hristovp/Key60/KiKad/Keyboard-60%/AlexandriaLibrary-master/graphics/acheronLongExtended.png

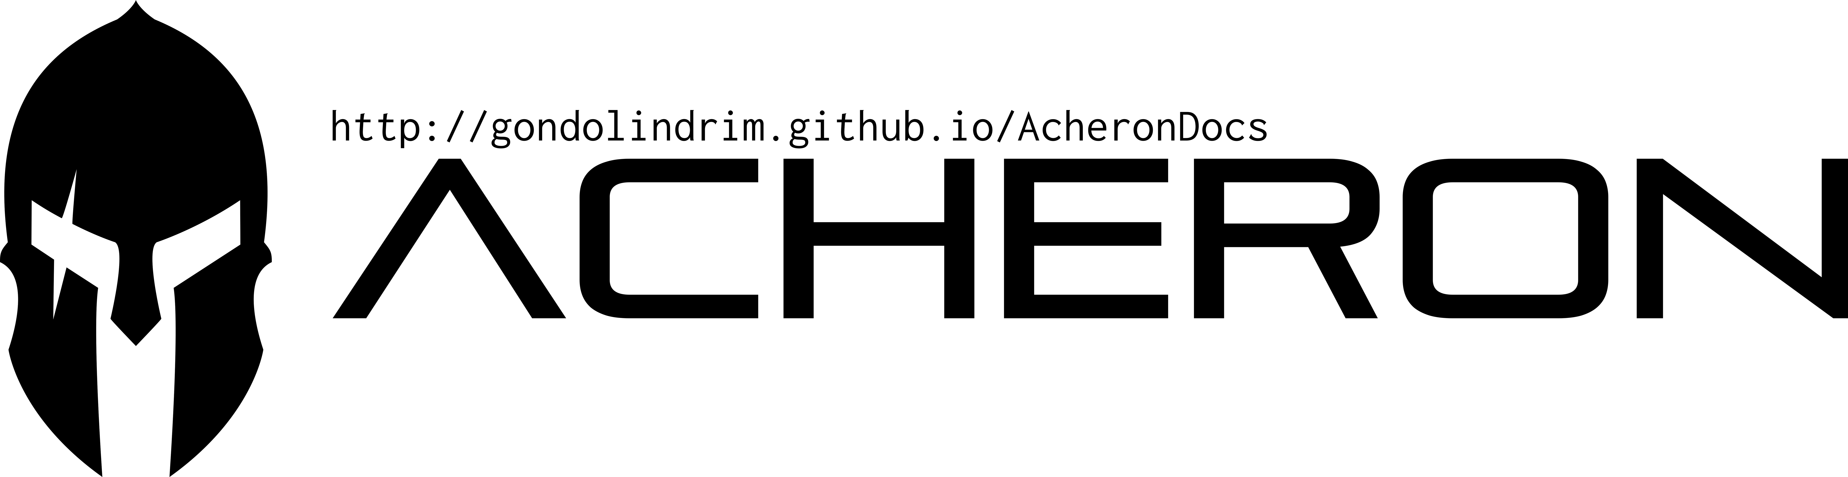
KiKad/Keyboard-60%/AlexandriaLibrary-master/graphics/acheronLongExtended.png
