hristovp/Key60/KiKad/Keyboard-60%/AlexandriaLibrary-master/graphics/acheronReadme.png

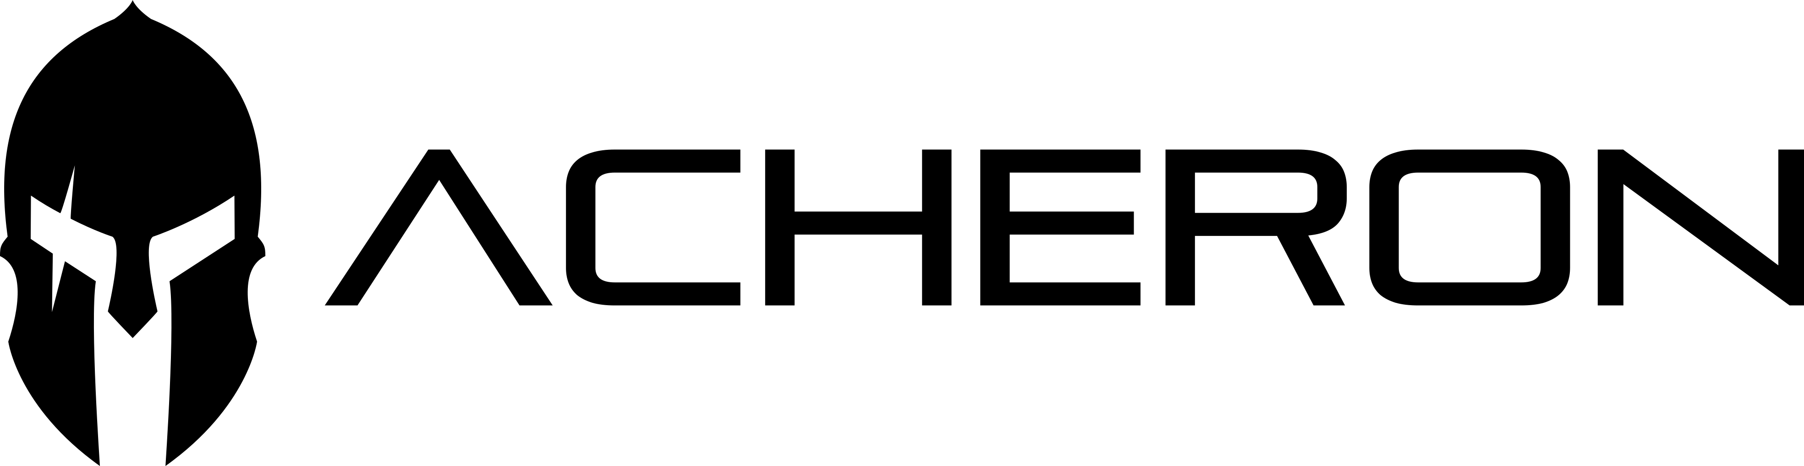
KiKad/Keyboard-60%/AlexandriaLibrary-master/graphics/acheronReadme.png
