hristovp/Key60/KiKad/Keyboard-60%/AlexandriaLibrary-master/graphics/acheronShort.png

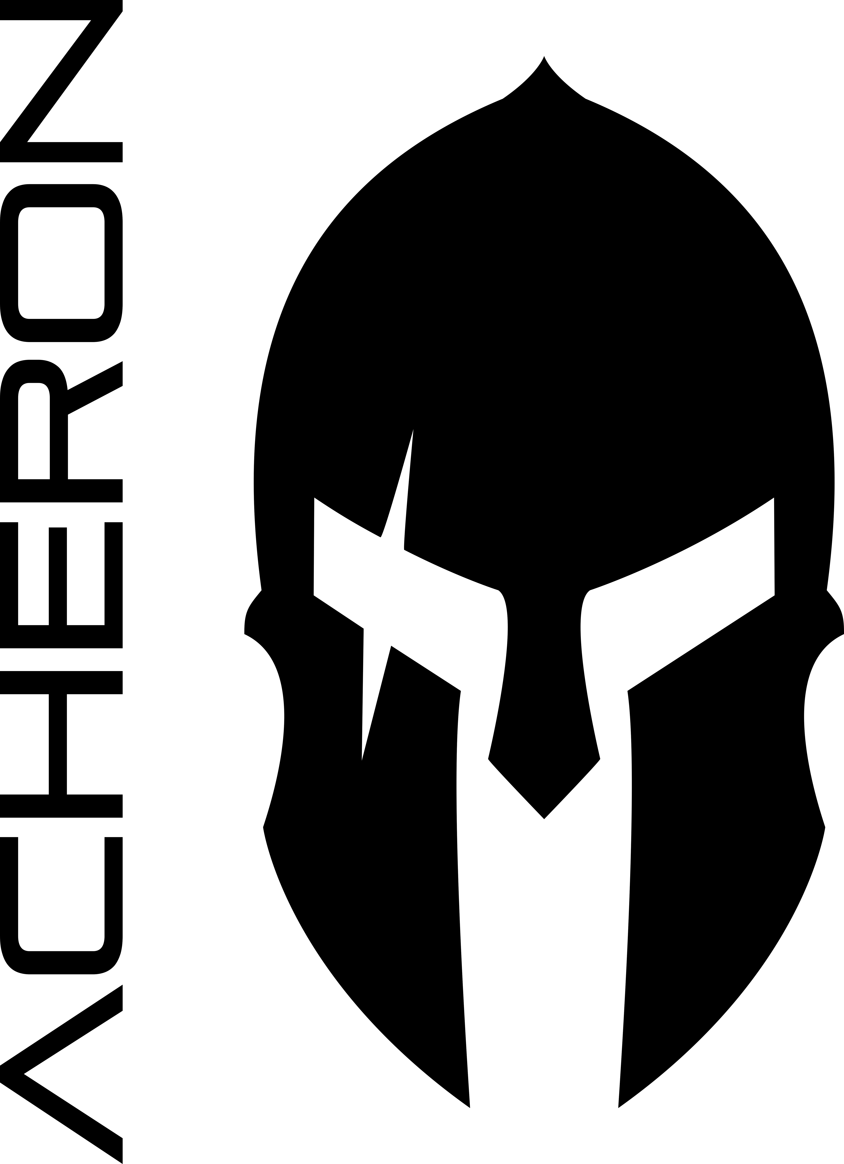
KiKad/Keyboard-60%/AlexandriaLibrary-master/graphics/acheronShort.png
