hristovp/Key60/KiKad/Keyboard-60%/AlexandriaLibrary-master/graphics/e6c1209rgb.png

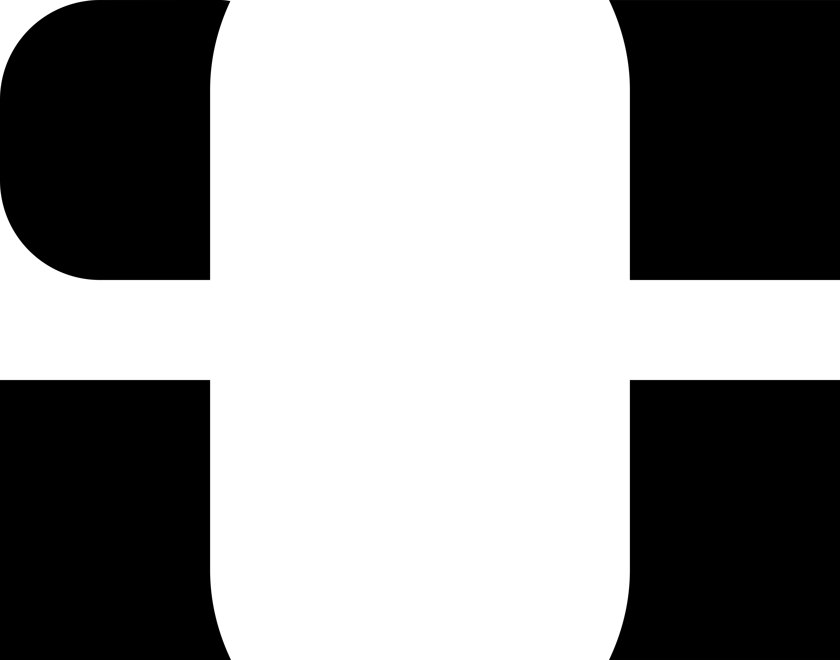
KiKad/Keyboard-60%/AlexandriaLibrary-master/graphics/e6c1209rgb.png
