hristovp/Key60/KiKad/Keyboard-60%/AlexandriaLibrary-master/graphics/shock_sign.png

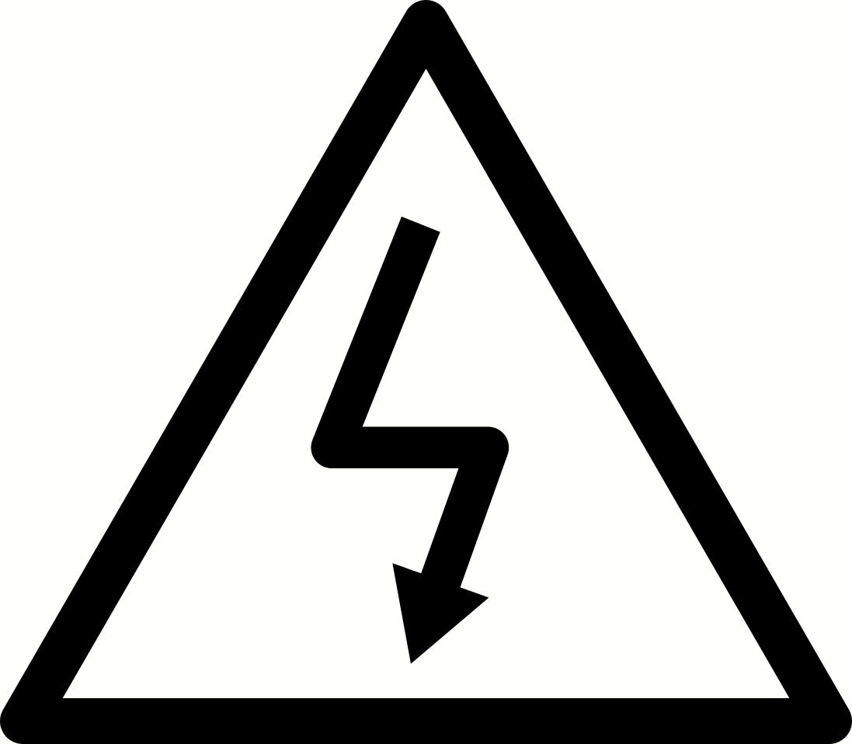
KiKad/Keyboard-60%/AlexandriaLibrary-master/graphics/shock_sign.png
