hristovp/Key60/KiKad/Keyboard-60%/AlexandriaLibrary-master/graphics/warning_sign.png

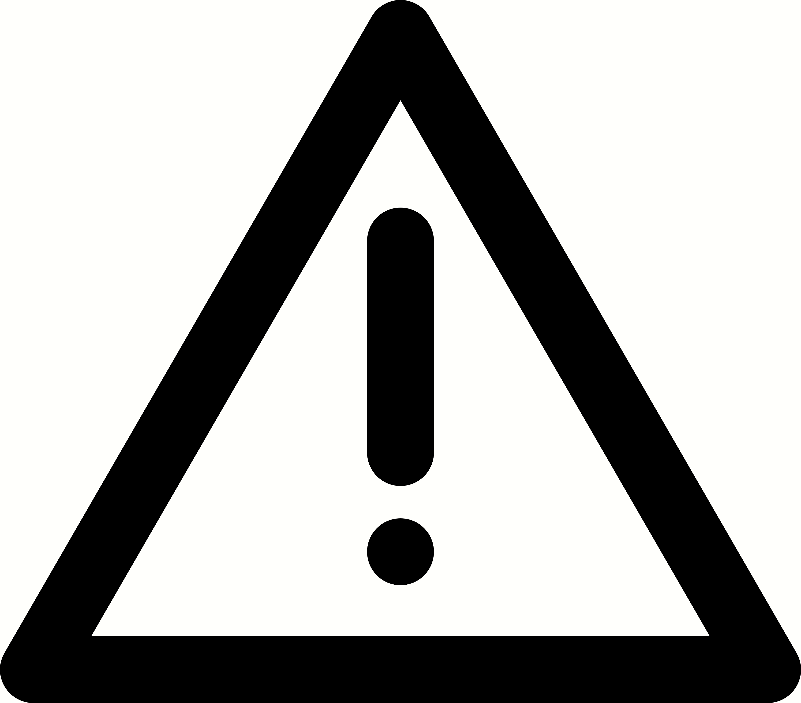
KiKad/Keyboard-60%/AlexandriaLibrary-master/graphics/warning_sign.png
