hristovp/Key60/KiKad/Keyboard-60%/AlexandriaLibrary-master/svgs/halfSideHole.png

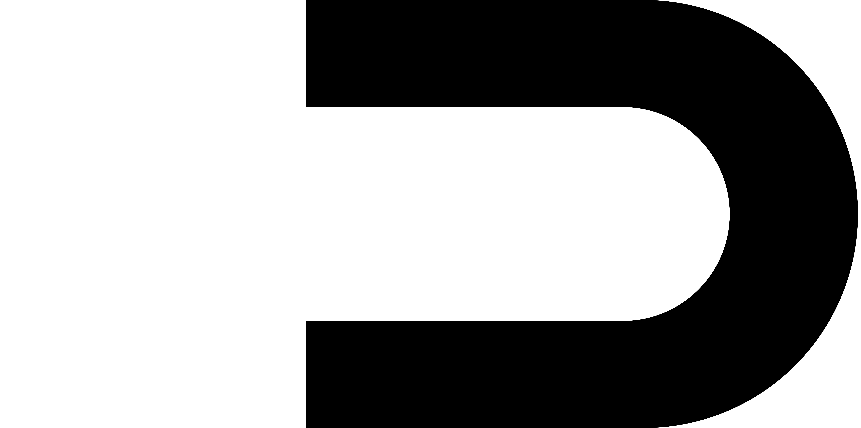
KiKad/Keyboard-60%/AlexandriaLibrary-master/svgs/halfSideHole.png
