hristovp/Key60/KiKad/Keyboard-60%/AlexandriaLibrary-master/svgs/ovalHole.png

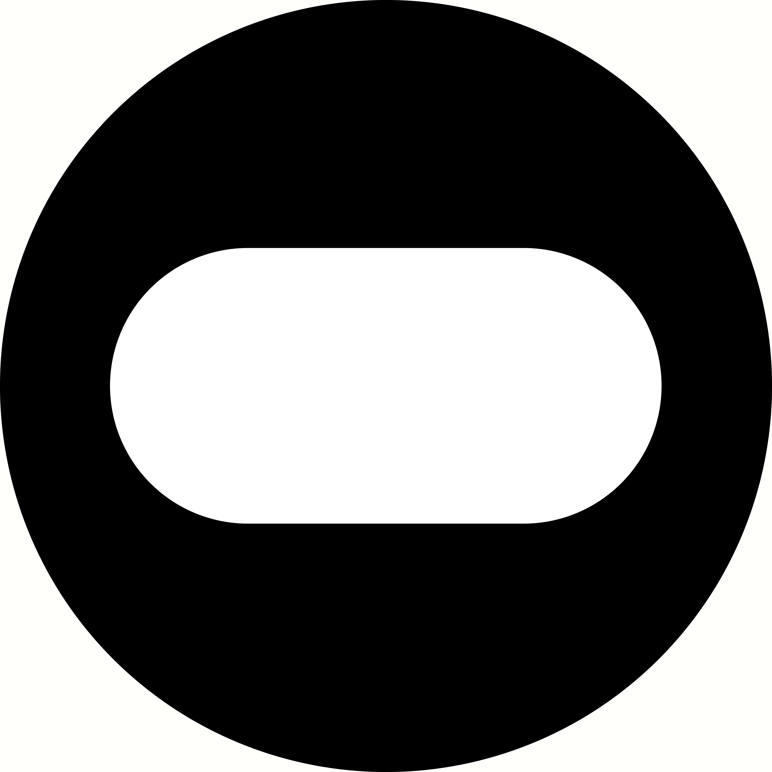
KiKad/Keyboard-60%/AlexandriaLibrary-master/svgs/ovalHole.png
