hristovp/Key60/KiKad/Keyboard-60%/AlexandriaLibrary-master/svgs/sideHole.png

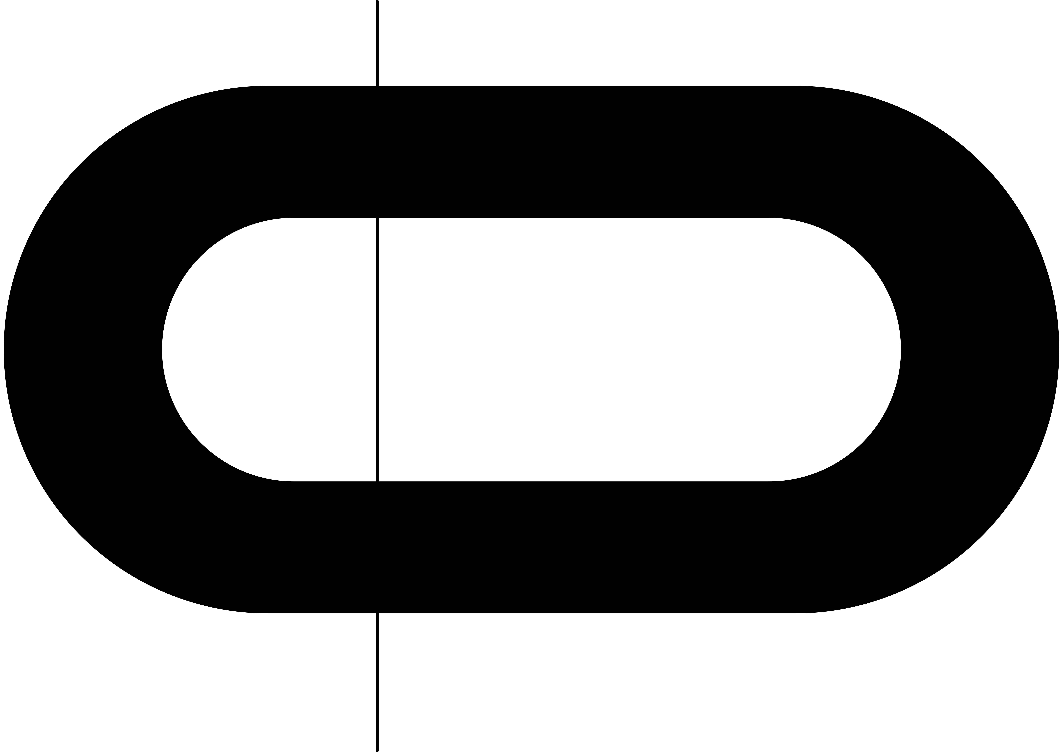
KiKad/Keyboard-60%/AlexandriaLibrary-master/svgs/sideHole.png
