hristovp/Key60/KiKad/Keyboard-60%/cherry-plate-mount-stabilizer-1.snapshot.5/stabil3.bmp

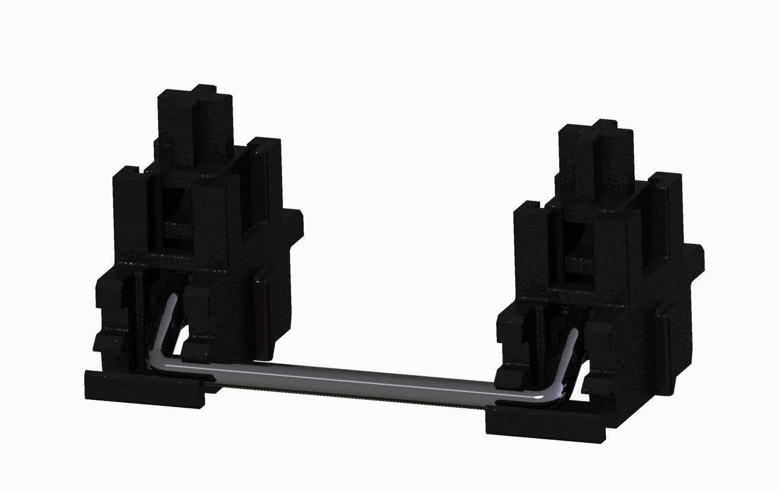
KiKad/Keyboard-60%/cherry-plate-mount-stabilizer-1.snapshot.5/stabil3.bmp
