hristovp/Key60/KiKad/Keyboard-60%/img/cat1467410768667.png.ff3f7331aa8d5c62bf9b5040716ce16c.thumb.png.339970b88bf1293ce4fa12bc12f244e9.png

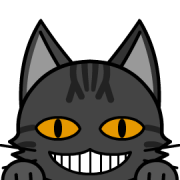
KiKad/Keyboard-60%/img/cat1467410768667.png.ff3f7331aa8d5c62bf9b5040716ce16c.thumb.png.339970b88bf1293ce4fa12bc12f244e9.png
