hristovp/Key60/KiKad/Keyboard-60%/img/cube.png

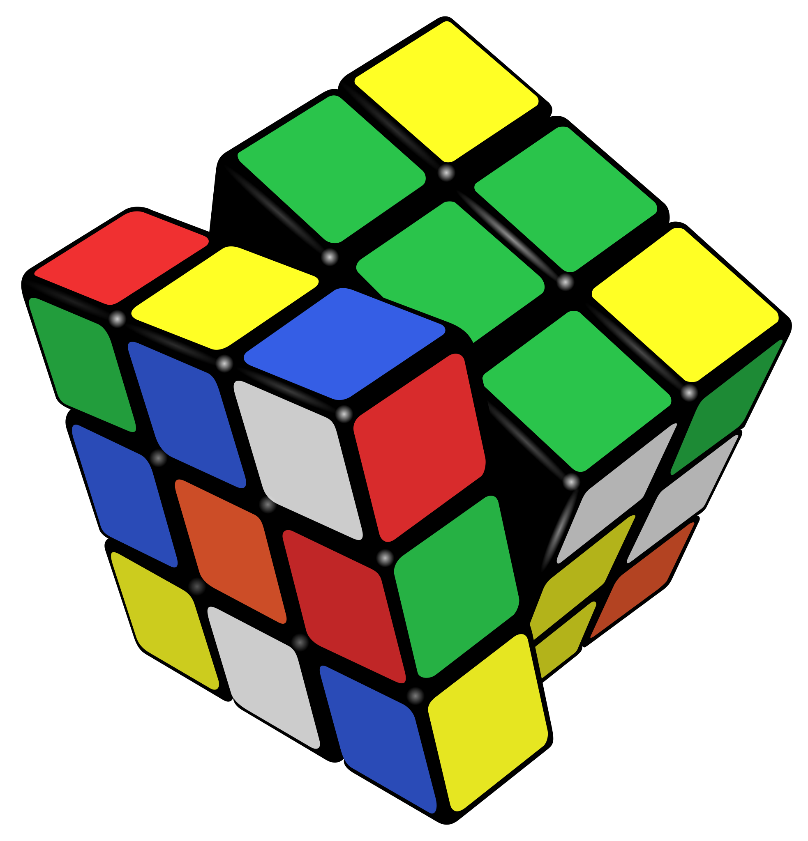
KiKad/Keyboard-60%/img/cube.png
