hristovp/Key60/KiKad/Keyboard-60%/AlexandriaLibrary-master/3d_models/OSC5032.STEP

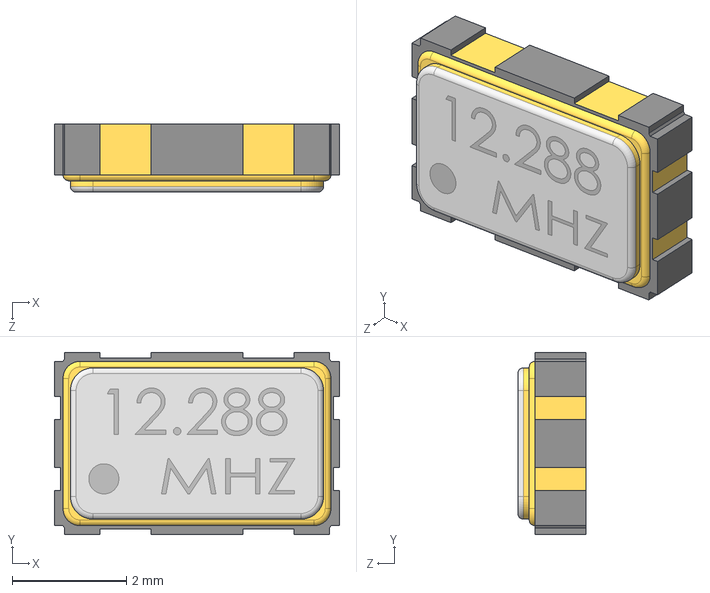
[picture p37: CAD file, 2022-08-21]
KiKad/Keyboard-60%/AlexandriaLibrary-master/3d_models/OSC5032.STEP
5.00 x 3.20 x 1.20 mm
