hristovp/Key60/KiKad/Keyboard-60%/AlexandriaLibrary-master/3d_models/WS2812.stp

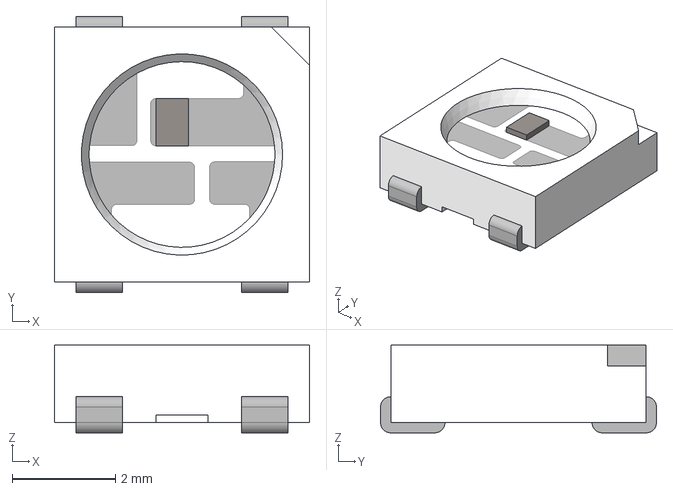
[picture p39: CAD file, 2022-08-21]
KiKad/Keyboard-60%/AlexandriaLibrary-master/3d_models/WS2812.stp
4.95 x 5.35 x 1.70 mm
