hristovp/Key60/KiKad/Keyboard-60%/AlexandriaLibrary-master/3d_models/wurth_632723300011.stp

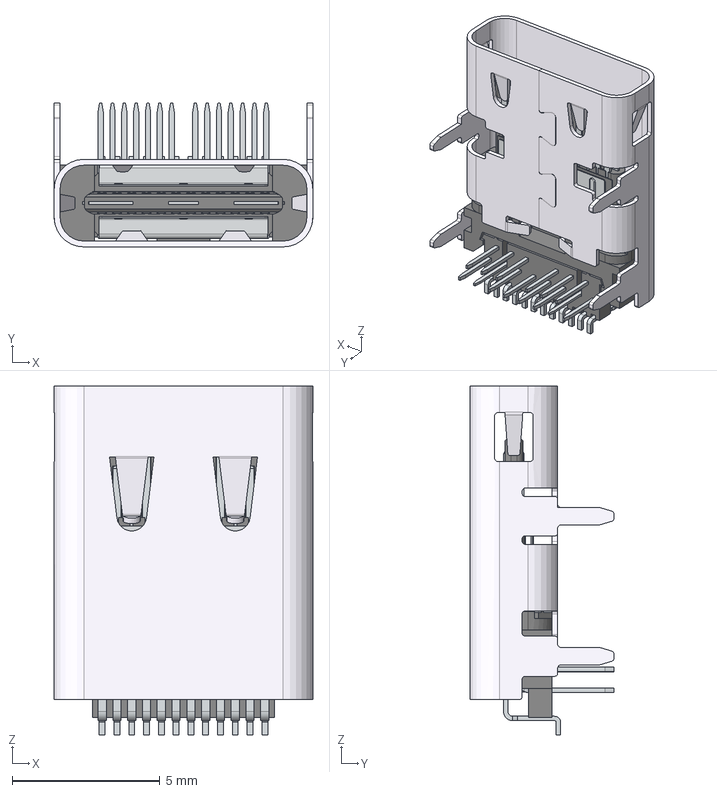
[picture p40: CAD file, 2022-08-21]
KiKad/Keyboard-60%/AlexandriaLibrary-master/3d_models/wurth_632723300011.stp
8.74 x 4.86 x 11.8 mm
632723300011_Housing
632723300011_Shielding_3_v3
632723300011_PIN2_Top_v3 x 8
632723300011_Housing_TOP
632723300011_Shielding_1_v3
632723300011_PIN1_Top_v3 x 4
632723300011_Housing_Bottom
632723300011_PIN1_Bottom_v3
632723300011_PIN2_Bottom_v3
632723300011_PIN4_Bottom_v3
632723300011_PIN5_Bottom_v3
632723300011_PIN6_Bottom_v3
632723300011_PIN7_Bottom_v3
632723300011_Shielding_2 x 2
632723300011_PIN1_Bottom_v3_mir
632723300011_PIN4_Bottom_v3_mir
632723300011_PIN6_Bottom_v3_mir
632723300011_PIN2_Bottom_v3_mir
632723300011_PIN5_Bottom_v3_mir
632723300011_PIN7_Bottom_v3_mir
632723300011_Housing_Bottom3
