hristovp/Key60/KiKad/Keyboard-60%/AlexandriaLibrary-master/3d_models/4PinHeader.step

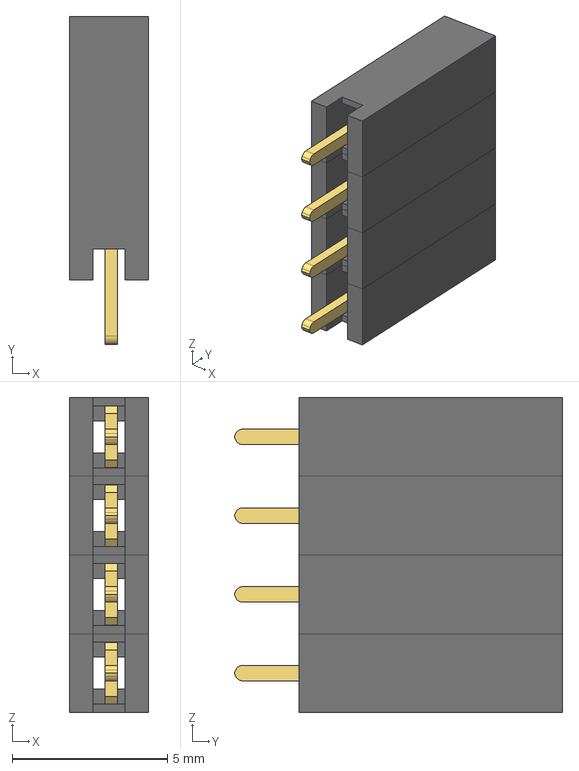
[picture p41: CAD file, 2022-08-21]
KiKad/Keyboard-60%/AlexandriaLibrary-master/3d_models/4PinHeader.step
2.54 x 10.6 x 10.2 mm
header-1 x 4
pin-1 x 4
