hristovp/Key60/KiKad/Keyboard-60%/AlexandriaLibrary-master/3d_models/6028SMDRGB.iges

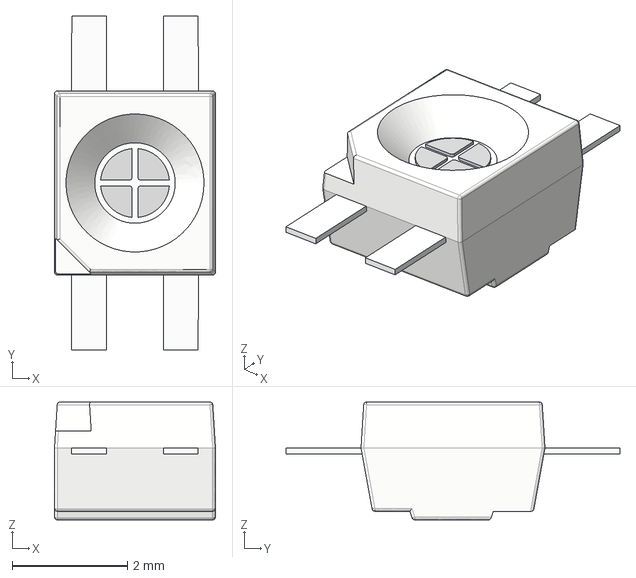
[picture p42: CAD file, 2022-08-21]
KiKad/Keyboard-60%/AlexandriaLibrary-master/3d_models/6028SMDRGB.iges
2.80 x 5.80 x 2.05 mm
