hristovp/Key60/KiKad/Keyboard-60%/AlexandriaLibrary-master/3d_models/RKJXT1F42001.step

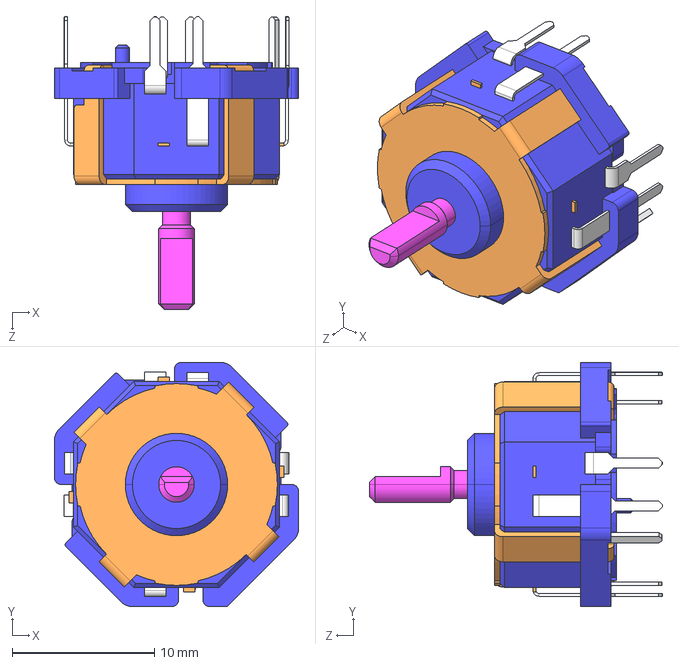
[picture p43: CAD file, 2022-08-21]
KiKad/Keyboard-60%/AlexandriaLibrary-master/3d_models/RKJXT1F42001.step
17.2 x 17.2 x 20.6 mm
