hristovp/Key60/KiKad/Keyboard-60%/AlexandriaLibrary-master/3d_models/BM04B-ASRS-TF.STEP

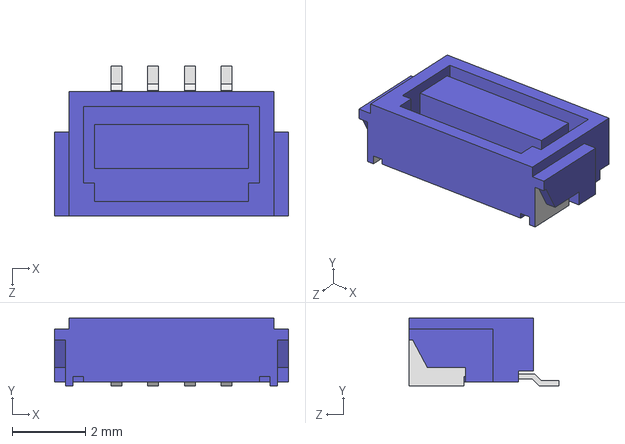
[picture p44: CAD file, 2022-08-21]
KiKad/Keyboard-60%/AlexandriaLibrary-master/3d_models/BM04B-ASRS-TF.STEP
6.40 x 1.85 x 4.10 mm
