hristovp/Key60/KiKad/Keyboard-60%/AlexandriaLibrary-master/3d_models/FUSE_1812.STEP

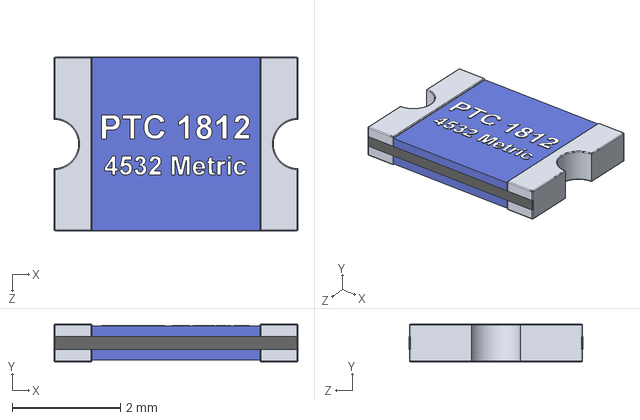
[picture p45: CAD file, 2022-08-21]
KiKad/Keyboard-60%/AlexandriaLibrary-master/3d_models/FUSE_1812.STEP
4.50 x 0.7 x 3.20 mm
