hristovp/Key60/KiKad/Keyboard-60%/AlexandriaLibrary-master/3d_models/male6PinHeader.stp

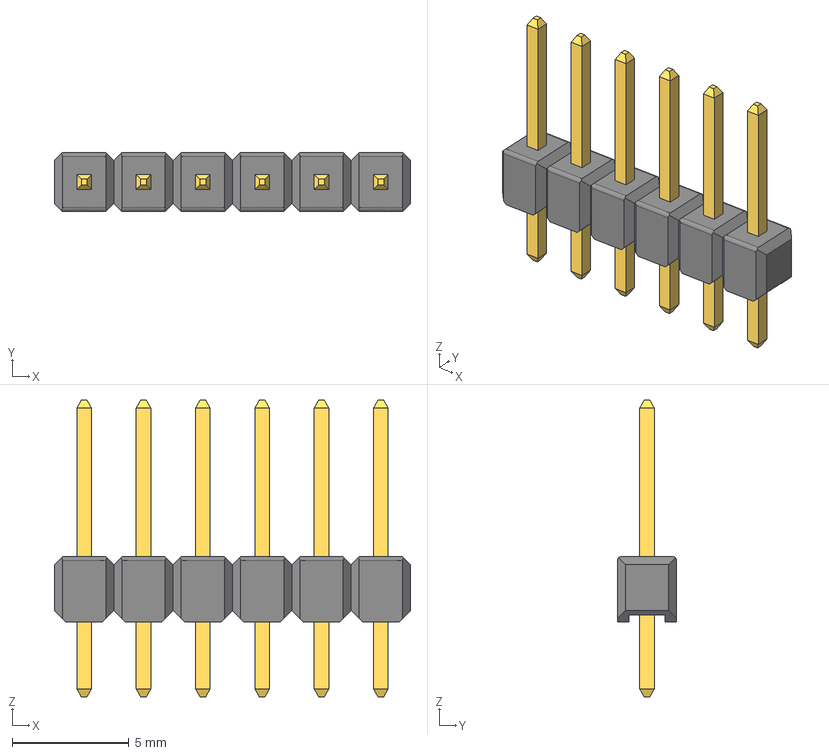
[picture p46: CAD file, 2022-08-21]
KiKad/Keyboard-60%/AlexandriaLibrary-master/3d_models/male6PinHeader.stp
15.2 x 2.54 x 12.7 mm
