hristovp/Key60/KiKad/Keyboard-60%/AlexandriaLibrary-master/3d_models/5032_XTAL.step

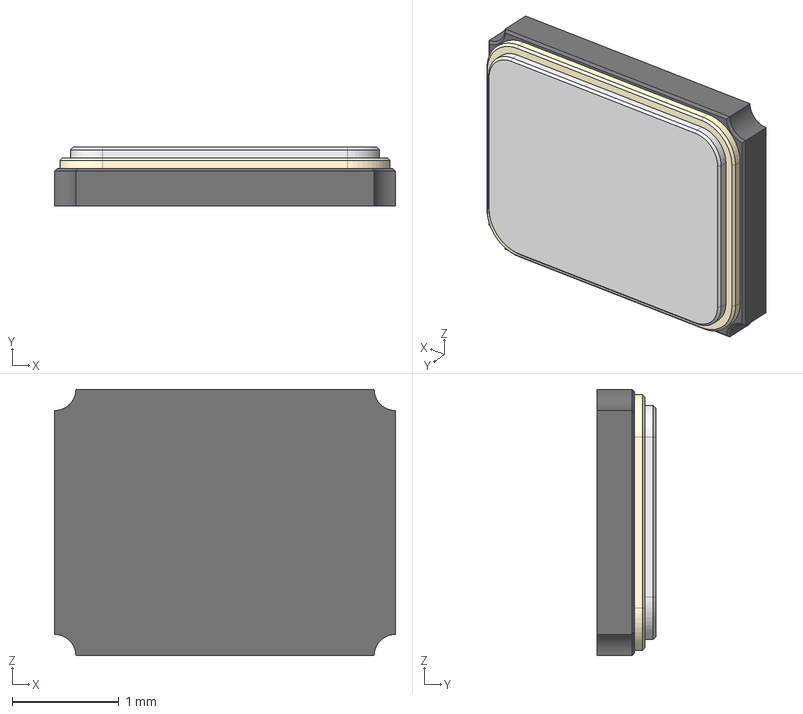
[picture p47: CAD file, 2022-08-21]
KiKad/Keyboard-60%/AlexandriaLibrary-master/3d_models/5032_XTAL.step
3.20 x 0.55 x 2.50 mm
