hristovp/Key60/KiKad/Keyboard-60%/AlexandriaLibrary-master/3d_models/Tactile_SMD_PushBtn_5x5mm.STEP

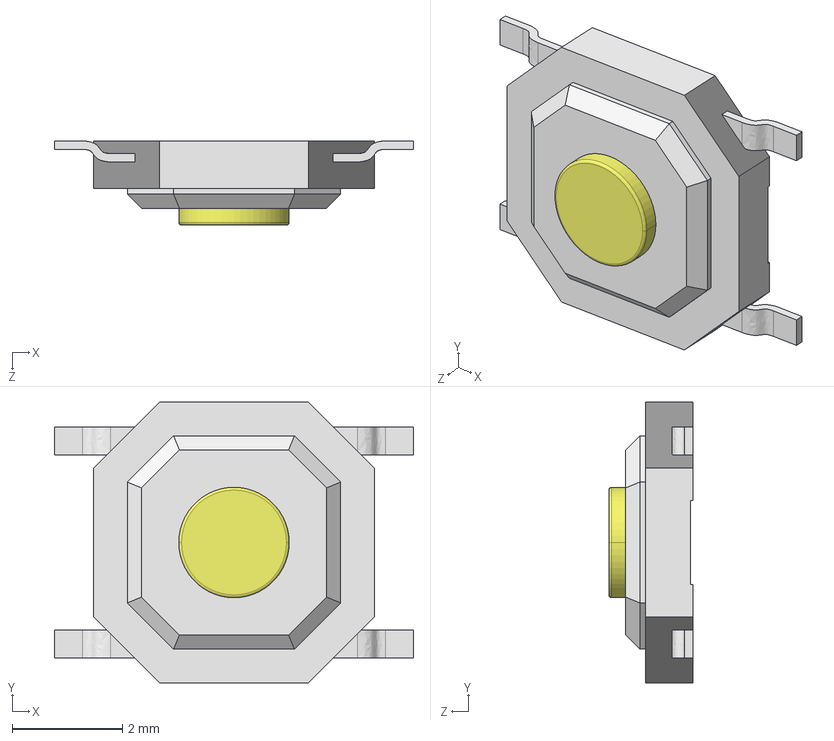
[picture p48: CAD file, 2022-08-21]
KiKad/Keyboard-60%/AlexandriaLibrary-master/3d_models/Tactile_SMD_PushBtn_5x5mm.STEP
6.50 x 5.08 x 1.52 mm
