hristovp/Key60/KiKad/Keyboard-60%/AlexandriaLibrary-master/3d_models/3313J-1-202E.stp

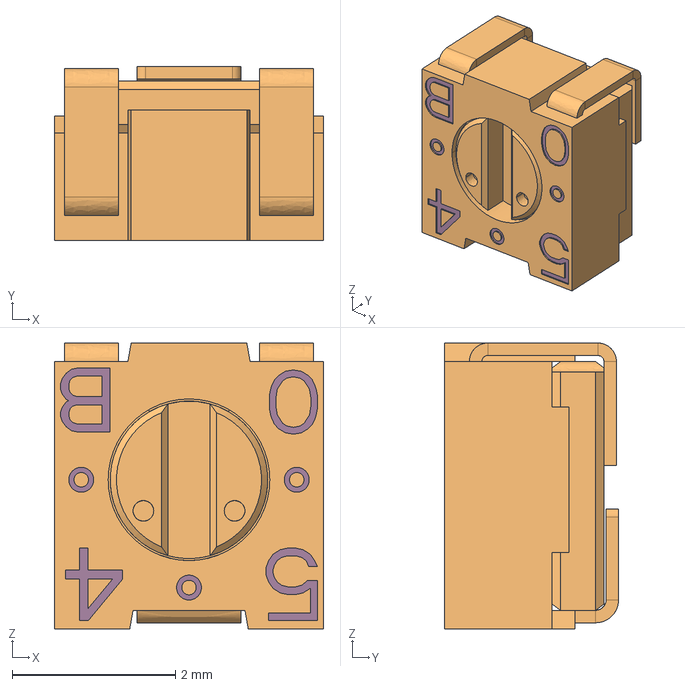
[picture p49: CAD file, 2022-08-21]
KiKad/Keyboard-60%/AlexandriaLibrary-master/3d_models/3313J-1-202E.stp
3.30 x 2.13 x 3.51 mm
