hristovp/Key60/KiKad/Keyboard-60%/AlexandriaLibrary-master/3d_models/SM14B-SRSS-TB.STEP

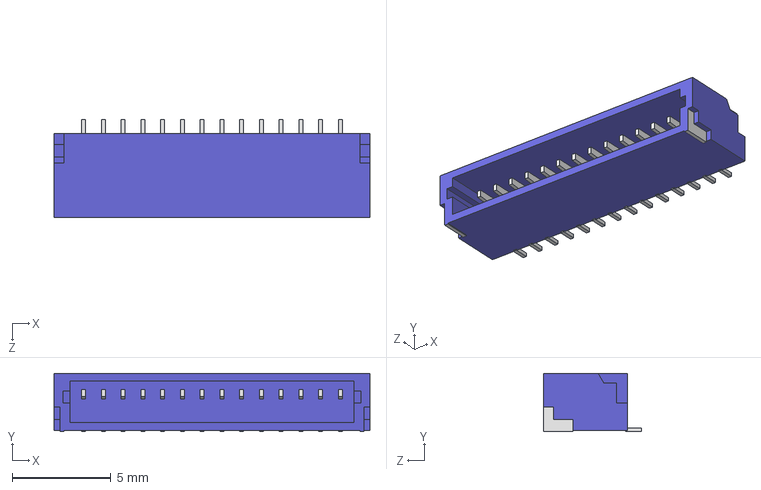
[picture p50: CAD file, 2022-08-21]
KiKad/Keyboard-60%/AlexandriaLibrary-master/3d_models/SM14B-SRSS-TB.STEP
16.0 x 2.96 x 4.95 mm
