hristovp/Key60/KiKad/Keyboard-60%/AlexandriaLibrary-master/3d_models/TE-1744426-4.stp

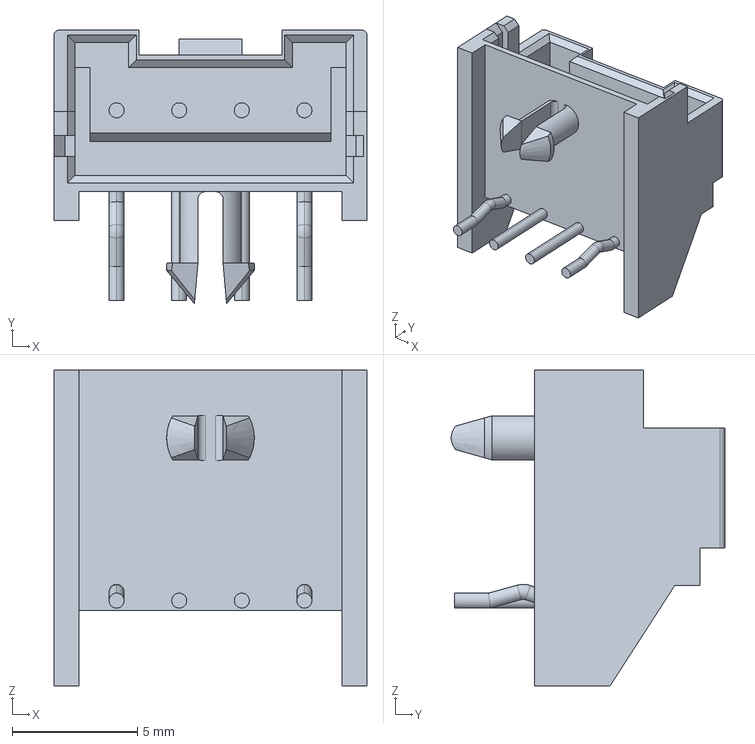
[picture p51: CAD file, 2022-08-21]
KiKad/Keyboard-60%/AlexandriaLibrary-master/3d_models/TE-1744426-4.stp
12.5 x 10.9 x 12.6 mm
