hristovp/Key60/KiKad/Keyboard-60%/AlexandriaLibrary-master/3d_models/ALPS_EC11E.stp

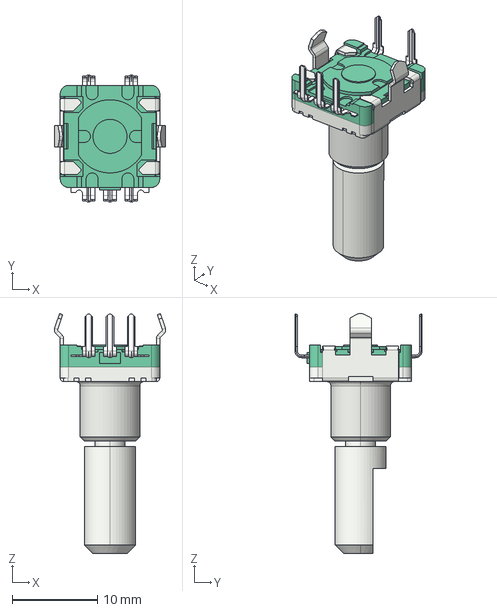
[picture p52: CAD file, 2022-08-21]
KiKad/Keyboard-60%/AlexandriaLibrary-master/3d_models/ALPS_EC11E.stp
13.1 x 15.0 x 28.2 mm
