hristovp/Key60/KiKad/Keyboard-60%/AlexandriaLibrary-master/3d_models/MDBT40.step

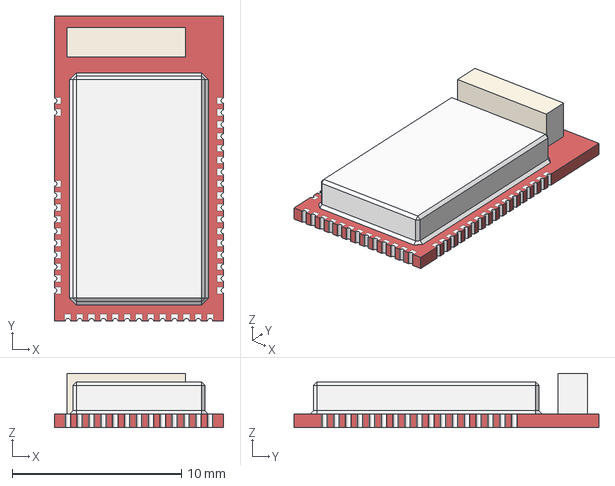
[picture p53: CAD file, 2022-08-21]
KiKad/Keyboard-60%/AlexandriaLibrary-master/3d_models/MDBT40.step
10.0 x 18.0 x 3.20 mm
