hristovp/Key60/KiKad/Keyboard-60%/AlexandriaLibrary-master/3d_models/keystone-PN3030TR.STEP

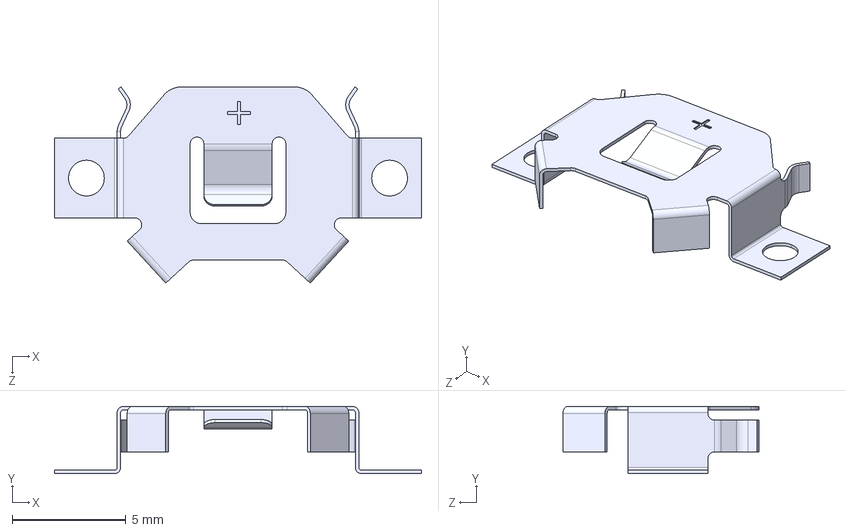
[picture p54: CAD file, 2022-08-21]
KiKad/Keyboard-60%/AlexandriaLibrary-master/3d_models/keystone-PN3030TR.STEP
16.1 x 2.95 x 8.61 mm
