hristovp/Key60/KiKad/Keyboard-60%/AlexandriaLibrary-master/3d_models/angle4PinHeader.step

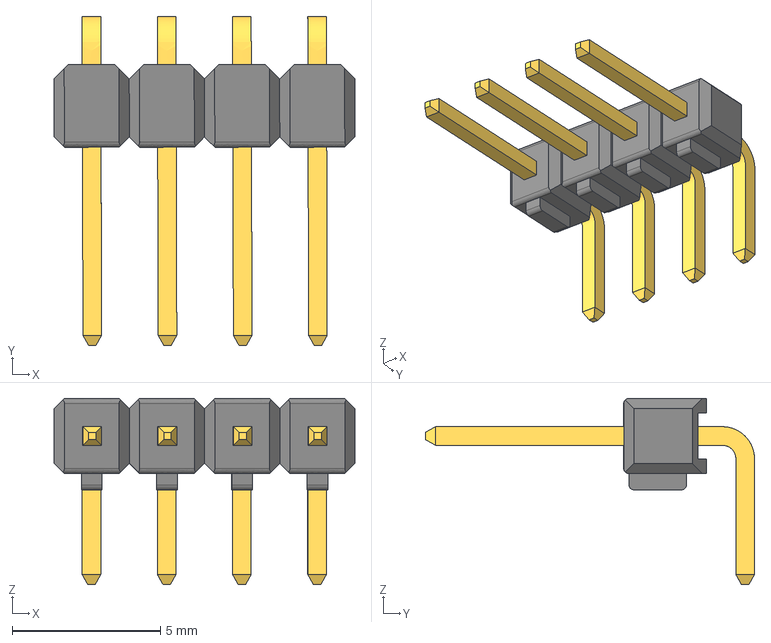
[picture p56: CAD file, 2022-08-21]
KiKad/Keyboard-60%/AlexandriaLibrary-master/3d_models/angle4PinHeader.step
10.2 x 11.1 x 6.29 mm
