hristovp/Key60/KiKad/Keyboard-60%/AlexandriaLibrary-master/3d_models/angle6PinHeader.stp

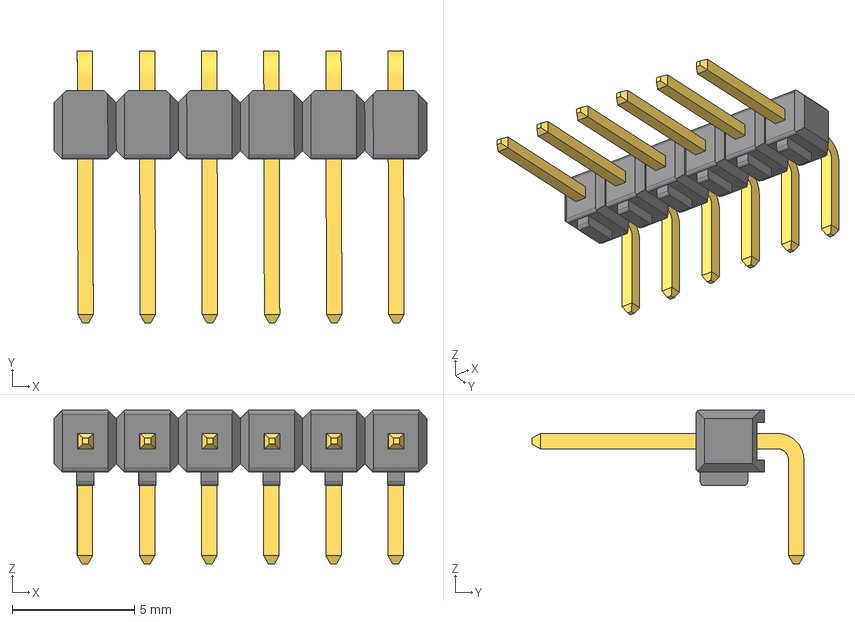
[picture p57: CAD file, 2022-08-21]
KiKad/Keyboard-60%/AlexandriaLibrary-master/3d_models/angle6PinHeader.stp
15.2 x 11.1 x 6.29 mm
