hristovp/Key60/KiKad/Keyboard-60%/AlexandriaLibrary-master/3d_models/UX60SC-MB-5S8.stp

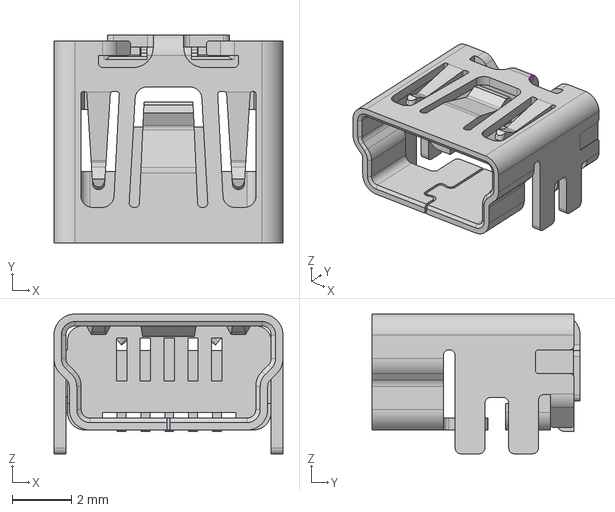
[picture p58: CAD file, 2022-08-21]
KiKad/Keyboard-60%/AlexandriaLibrary-master/3d_models/UX60SC-MB-5S8.stp
7.70 x 7.00 x 4.70 mm
