hristovp/Key60/KiKad/Keyboard-60%/AlexandriaLibrary-master/3d_models/TYPE-C-31-M-14.step

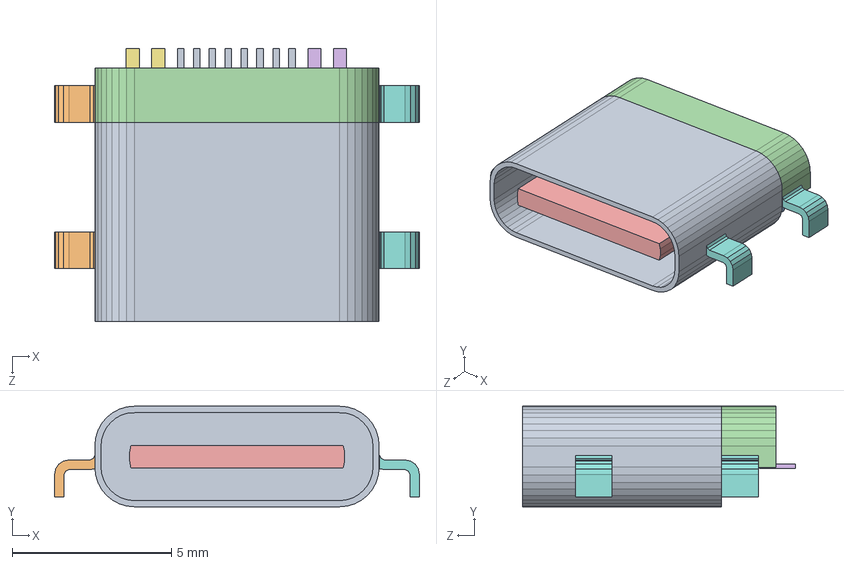
[picture p59: CAD file, 2022-08-21]
KiKad/Keyboard-60%/AlexandriaLibrary-master/3d_models/TYPE-C-31-M-14.step
11.5 x 3.16 x 8.58 mm
