hristovp/Key60/KiKad/Keyboard-60%/AlexandriaLibrary-master/3d_models/XM7D-0512.STEP

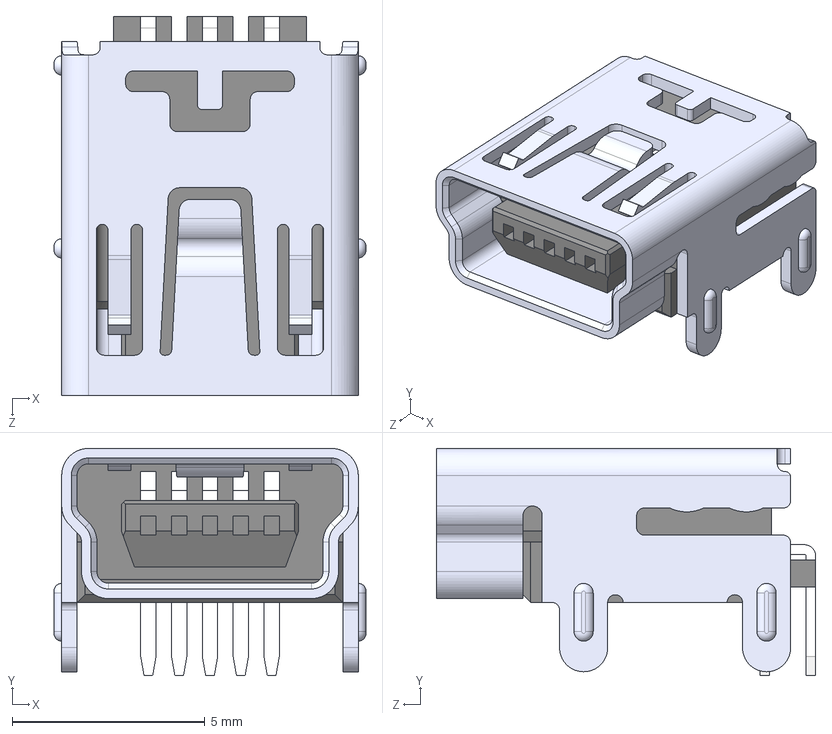
[picture p60: CAD file, 2022-08-21]
KiKad/Keyboard-60%/AlexandriaLibrary-master/3d_models/XM7D-0512.STEP
8.10 x 5.90 x 9.85 mm
