hristovp/Key60/KiKad/Keyboard-60%/AlexandriaLibrary-master/3d_models/SM04B-SRSS-TB.STEP

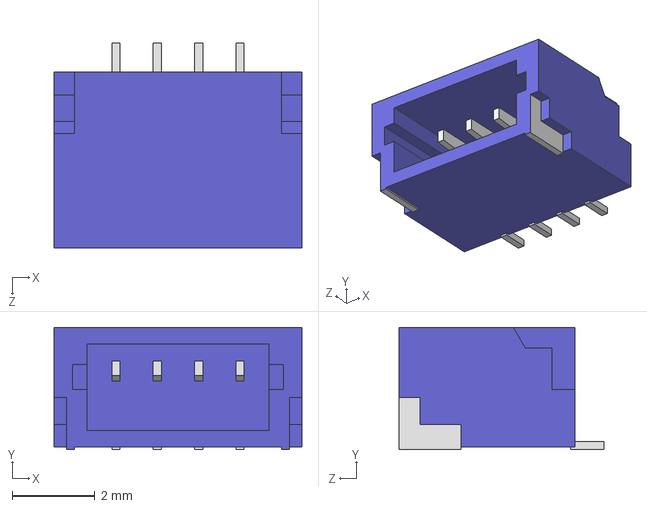
[picture p61: CAD file, 2022-08-21]
KiKad/Keyboard-60%/AlexandriaLibrary-master/3d_models/SM04B-SRSS-TB.STEP
6.00 x 2.96 x 4.95 mm
