hristovp/Key60/KiKad/Keyboard-60%/AlexandriaLibrary-master/3d_models/WS2812-Mini.step

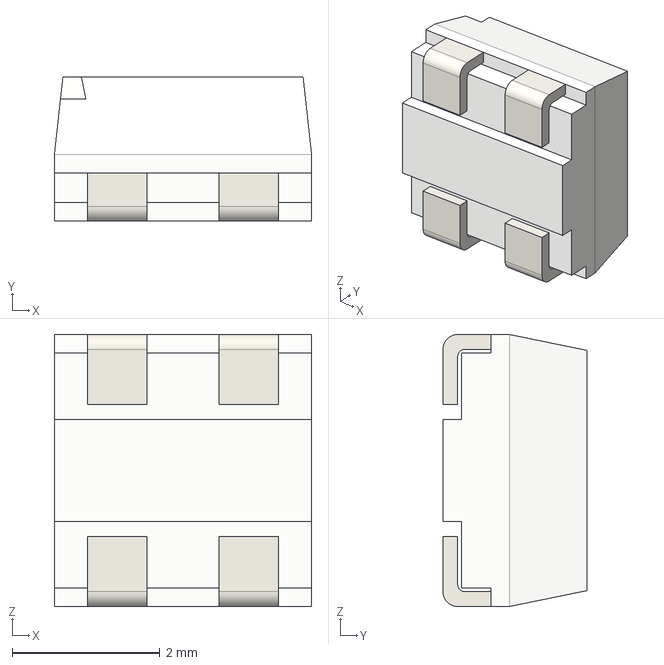
[picture p62: CAD file, 2022-08-21]
KiKad/Keyboard-60%/AlexandriaLibrary-master/3d_models/WS2812-Mini.step
3.48 x 1.95 x 3.68 mm
