hristovp/Key60/KiKad/Keyboard-60%/AlexandriaLibrary-master/3d_models/BM04B-SRSS.step

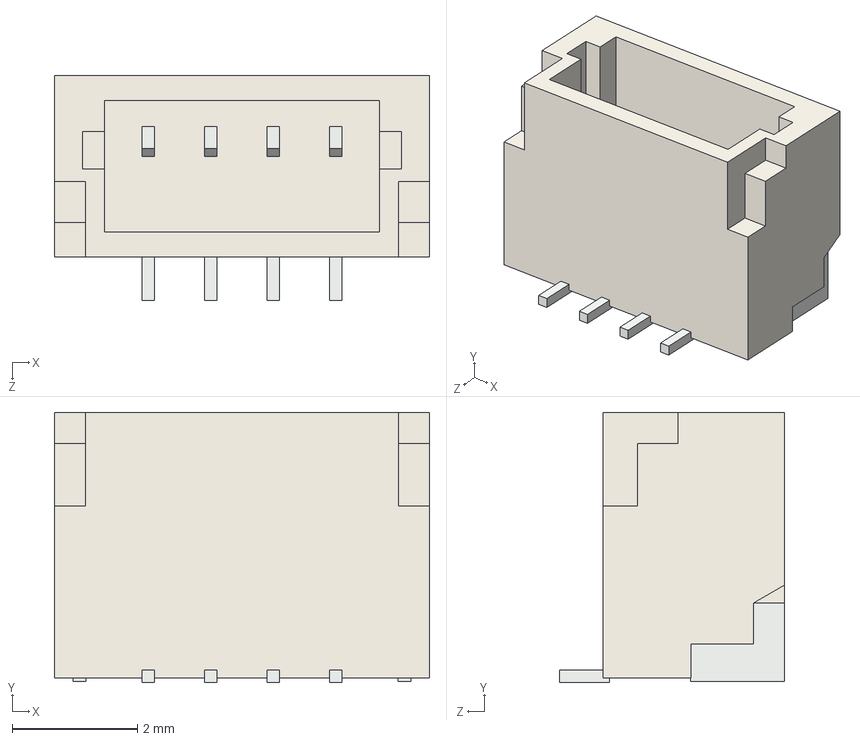
[picture p63: CAD file, 2022-08-21]
KiKad/Keyboard-60%/AlexandriaLibrary-master/3d_models/BM04B-SRSS.step
6.00 x 4.32 x 3.60 mm
