hristovp/Key60/KiKad/Keyboard-60%/AlexandriaLibrary-master/3d_models/SM11B-SRSS-TB.STEP

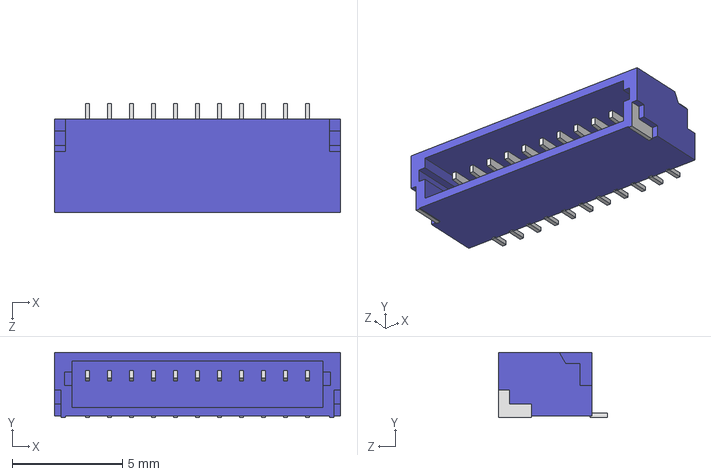
[picture p64: CAD file, 2022-08-21]
KiKad/Keyboard-60%/AlexandriaLibrary-master/3d_models/SM11B-SRSS-TB.STEP
13.0 x 2.96 x 4.95 mm
