hristovp/Key60/KiKad/Keyboard-60%/AlexandriaLibrary-master/3d_models/kailh_socket_mx.stp

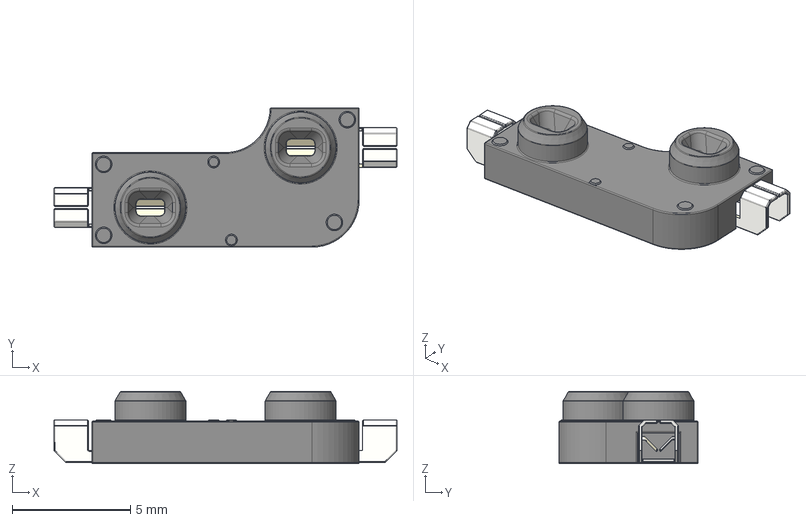
[picture p65: CAD file, 2022-08-21]
KiKad/Keyboard-60%/AlexandriaLibrary-master/3d_models/kailh_socket_mx.stp
14.5 x 5.89 x 3.05 mm
