hristovp/Key60/KiKad/Keyboard-60%/AlexandriaLibrary-master/3d_models/TE-2132415-4.stp

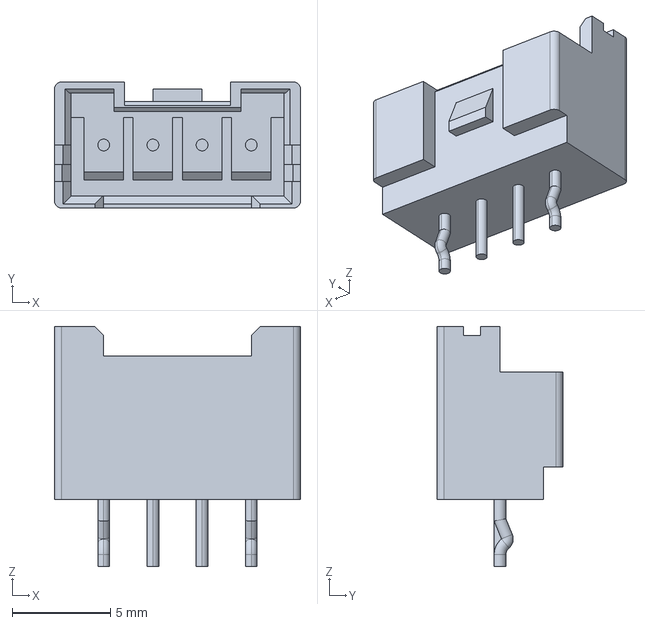
[picture p66: CAD file, 2022-08-21]
KiKad/Keyboard-60%/AlexandriaLibrary-master/3d_models/TE-2132415-4.stp
12.5 x 6.40 x 12.2 mm
